EgeSarii/CoroneX/python_code/People-Counting-in-Real-Time-master/Run.py

from mylib.centroidtracker import CentroidTracker
from mylib.trackableobject import TrackableObject
from imutils.video import VideoStream
from imutils.video import FPS
from mylib.mailer import Mailer
from mylib import config, thread
import time, schedule, csv
import numpy as np
import argparse, imutils
import time, dlib, cv2, datetime
from itertools import zip_longest
import Adafruit_DHT
import serial

#co2
import board
import busio
import webbrowser, os, sys


import tkinter as tk

mx=""
my=""
mz=""
ml=""
mu=""

def send():
    global mx,my,mz,ml,mu
    mx=mailField.get()
    my=passField.get()
    mz=sendField.get()
    ml=peopleField.get()
    mu=urlField.get()
    
def startUpWebsites():
    url = "http://192.168.1.156/"

    chrome_path = '/usr/lib/chromium-browser/chromium-browser'
    webbrowser.get(chrome_path).open(url)



#humidity and temperature of the place

t0 = time.time()

def run():
    global mailField,passField, sendField, peopleField, urlField
    mailSender = Mailer()
    
    root = tk.Tk()
    root.configure(bg = '#f4b9b9')
    
    max_amount = 0
    label1 = None #just so it is defined
    label1 = tk.Button(root,text ="START UP HUMIDITY AND TEMPERATURE ENVIRONMENT SETTINGS + AIR QUALITY SENSOR",command = startUpWebsites)
    label1.grid(row=0, column= 1)
    labelMail = tk.Label(root, text="User mail: ")
    labelMail.grid(row=1,column=0)
    labelPass = tk.Label(root, text="User password: ")
    labelPass.grid(row=2,column=0)
    labelSend = tk.Label(root, text="Send to Mail: ")
    labelSend.grid(row=3,column=0)
    labelPeople = tk.Label(root, text="People Limit: ")
    labelPeople.grid(row=4,column=0)
    urlLabel=tk.Label(root, text="IP Cam URL: ")
    urlLabel.grid(row=5,column=0)
    mailField=tk.Entry(root)
    mailField.grid(row=1,column=1,ipadx=100)
    passField=tk.Entry(root)
    passField.grid(row=2,column=1,ipadx=100)
    sendField=tk.Entry(root)
    sendField.grid(row=3,column=1,ipadx=100)
    peopleField=tk.Entry(root)
    peopleField.grid(row=4,column=1,ipadx=100)
    urlField=tk.Entry(root)
    urlField.grid(row=5,column=1,ipadx=100)
    submitValues=tk.Button(text="Submit Values!", command = send)
    submitValues.grid(row=6,column=1, ipadx = 50,padx = 50)
    root.update_idletasks()
    root.update()

    sendToMail = ""
    people_limit = ""
    ipCamUrl = ""

    while(mailSender.EMAIL == "" or mailSender.PASS == "" or sendToMail == "" or people_limit == "" ):
        mailSender.EMAIL=mx
        mailSender.PASS=my
        sendToMail=mz
        people_limit=ml
        ipCamUrl = mu
        root.update()
    
    labelSend.destroy()
    labelMail.destroy()
    labelPass.destroy()
    labelPeople.destroy()
    peopleField.destroy()
    mailField.destroy()
    passField.destroy()
    sendField.destroy()
    submitValues.destroy()
    urlField.destroy()
    urlLabel.destroy()
    label1.destroy()
    
    ct = 0
    counter = tk.Label(root, text = "PEOPLE INSIDE: " + str(ct), width = 1000,bg='White')
    counter.pack(side= 'top' , pady = 80)
    counter.config(font =("Courier",44))

    
    
    enter = tk.Label(root, text = "ENTERING ALLOWED", width = 1000,fg="SpringGreen",bg='White')
    enter.pack(side= 'bottom' , pady = 80)
    enter.config(font =("Courier",60))
  
    
    img = tk.PhotoImage(file="REPRES.png")
    canvas= tk.Label(root, image = img)
    canvas.pack(side ='bottom')
    
    root.attributes('-fullscreen', True)

    # construct the argument parse and parse the arguments
    ap = argparse.ArgumentParser()
    ap.add_argument("-p", "--prototxt", required=False,
        help="path to Caffe 'deploy' prototxt file")
    ap.add_argument("-m", "--model", required=True,
        help="path to Caffe pre-trained model")
    ap.add_argument("-i", "--input", type=str,
        help="path to optional input video file")
    ap.add_argument("-o", "--output", type=str,
        help="path to optional output video file")
    # confidence default 0.4
    ap.add_argument("-c", "--confidence", type=float, default=0.4,
        help="minimum probability to filter weak detections")
    ap.add_argument("-s", "--skip-frames", type=int, default=30,
        help="# of skip frames between detections")
    args = vars(ap.parse_args())

    # initialize the list of class labels MobileNet SSD was trained to
    # detect
    CLASSES = ["background", "aeroplane", "bicycle", "bird", "boat",
        "bottle", "bus", "car", "cat", "chair", "cow", "diningtable",
        "dog", "horse", "motorbike", "person", "pottedplant", "sheep",
        "sofa", "train", "tvmonitor"]

    # load our serialized model from disk
    net = cv2.dnn.readNetFromCaffe(args["prototxt"], args["model"])

    print("[INFO] Starting the video..")
    if(ipCamUrl == ""):
        vs = cv2.VideoCapture(args["input"])
    else:
        vs = cv2.VideoCapture(ipCamUrl)
    # initialize the video writer (we'll instantiate later if need be)
    writer = None

    # initialize the frame dimensions (we'll set them as soon as we read
    # the first frame from the video)
    W = None
    H = None

    # instantiate our centroid tracker, then initialize a list to store
    # each of our dlib correlation trackers, followed by a dictionary to
    # map each unique object ID to a TrackableObject
    ct = CentroidTracker(maxDisappeared=40, maxDistance=50)
    trackers = []
    trackableObjects = {}

    # initialize the total number of frames processed thus far, along
    # with the total number of objects that have moved either up or down
    #NUMBER PEOPLE
    totalFrames = 0
    totalDown = 0
    totalUp = 0
    x = []
    empty=[]
    empty1=[]

    # start the frames per second throughput estimator
    fps = FPS().start()

    if config.Thread:
        vs = thread.ThreadingClass(config.url)

    # loop over frames from the video stream
    ser = serial.Serial('/dev/ttyACM0', 9600)
    while True:
        data = ser.readline().decode('ascii')
        oldSum = sum(x)
        t_end= time.time() + 16
        if(float(data)>=30.5 and float(data)<= 32.5):
                nowImg = tk.PhotoImage(file="download.png")
                canvas.configure(image= nowImg)                                                
                enter.configure(text = "ENTERING IS ALLOWED! :)", width = 1000,fg="SpringGreen")
                # grab the next frame and handle if we are reading from either
                # VideoCapture or VideoStream
                while time.time() < t_end:
                    frame = vs.read()
                    frame = frame[1] if args.get("input", False) else frame

                    # if we are viewing a video and we did not grab a frame then we
                    # have reached the end of the video
                    if args["input"] is not None and frame is None:
                        break

                    # resize the frame to have a maximum width of 500 pixels (the
                    # less data we have, the faster we can process it), then convert
                    # the frame from BGR to RGB for dlib
                    frame = imutils.resize(frame, width = 500)
                    rgb = cv2.cvtColor(frame, cv2.COLOR_BGR2RGB)
    
                    # if the frame dimensions are empty, set them
                    if W is None or H is None:
                        (H, W) = frame.shape[:2]

                    # if we are supposed to be writing a video to disk, initialize
                    # the writer
                    if args["output"] is not None and writer is None:
                        fourcc = cv2.VideoWriter_fourcc(*"MJPG")
                        writer = cv2.VideoWriter(args["output"], fourcc, 30,
                                    (W, H), True)

                    # initialize the current status along with our list of bounding
                    # box rectangles returned by either (1) our object detector or
                    # (2) the correlation trackers
                    status = "Waiting"
                    rects = []

                    # check to see if we should run a more computationally expensive
                    # object detection method to aid our tracker
                    if totalFrames % args["skip_frames"] == 0:
                        # set the status and initialize our new set of object trackers
                        status = "Detecting"
                        trackers = []

                        # convert the frame to a blob and pass the blob through the
                        # network and obtain the detections
                        blob = cv2.dnn.blobFromImage(frame, 0.007843, (W, H), 127.5)
                        net.setInput(blob)
                        detections = net.forward()

                        # loop over the detections
                        for i in np.arange(0, detections.shape[2]):
                                    # extract the confidence (i.e., probability) associated
                                    # with the prediction
                                    confidence = detections[0, 0, i, 2]

                                        # filter out weak detections by requiring a minimum
                                        # confidence
                                    if confidence > args["confidence"]:
                                        # extract the index of the class label from the
                                        # detections list
                                        idx = int(detections[0, 0, i, 1])

                                        # if the class label is not a person, ignore it
                                        if CLASSES[idx] != "person":
                                                    continue

                                        # compute the (x, y)-coordinates of the bounding box
                                        # for the object
                                        box = detections[0, 0, i, 3:7] * np.array([W, H, W, H])
                                        (startX, startY, endX, endY) = box.astype("int")


                                        # construct a dlib rectangle object from the bounding
                                        # box coordinates and then start the dlib correlation
                                        # tracker
                                        tracker = dlib.correlation_tracker()
                                        rect = dlib.rectangle(startX, startY, endX, endY)
                                        tracker.start_track(rgb, rect)

                                        # add the tracker to our list of trackers so we can
                                        # utilize it during skip frames
                                        trackers.append(tracker)

                    # otherwise, we should utilize our object *trackers* rather than
                    # object *detectors* to obtain a higher frame processing throughput
                    else:
                        # loop over the trackers
                        for tracker in trackers:
                                    # set the status of our system to be 'tracking' rather
                                    # than 'waiting' or 'detecting'
                                    status = "Tracking"

                                    # update the tracker and grab the updated position
                                    tracker.update(rgb)
                                    pos = tracker.get_position()

                                    # unpack the position object
                                    startX = int(pos.left())
                                    startY = int(pos.top())
                                    endX = int(pos.right())
                                    endY = int(pos.bottom())

                                    # add the bounding box coordinates to the rectangles lists
                                    rects.append((startX, startY, endX, endY))

                    # draw a horizontal line in the center of the frame -- once an
                    # object crosses this line we will determine whether they were
                    # moving 'up' or 'down'
                    cv2.line(frame, (0, H // 2), (W, H // 2), (0, 0, 0), 3)
                    cv2.putText(frame, "-Prediction border - Entrance-", (10, H - ((i * 20) + 200)),
                        cv2.FONT_HERSHEY_SIMPLEX, 0.5, (0, 0, 0), 1)

                    # use the centroid tracker to associate the (1) old object
                    # centroids with (2) the newly computed object centroids
                    objects = ct.update(rects)

                    # loop over the tracked objects
                    for (objectID, centroid) in objects.items():
                        # check to see if a trackable object exists for the current
                        # object ID
                        to = trackableObjects.get(objectID, None)

                        # if there is no existing trackable object, create one
                        if to is None:
                                    to = TrackableObject(objectID, centroid)

                        # otherwise, there is a trackable object so we can utilize it
                        # to determine direction
                        else:
                                    # the difference between the y-coordinate of the *current*
                                    # centroid and the mean of *previous* centroids will tell
                                    # us in which direction the object is moving (negative for
                                    # 'up' and positive for 'down')
                                    y = [c[1] for c in to.centroids]
                                    direction = centroid[1] - np.mean(y)
                                    to.centroids.append(centroid)

                                    # check to see if the object has been counted or not
                                    if not to.counted:
                                        # if the direction is negative (indicating the object
                                        # is moving up) AND the centroid is above the center
                                        # line, count the object
                                        if direction < 0 and centroid[1] < H // 2:
                                                    totalUp += 1
                                                    empty.append(totalUp)
                                                    to.counted = True

                                        # if the direction is positive (indicating the object
                                        # is moving down) AND the centroid is below the
                                        # center line, count the object
                                        elif direction > 0 and centroid[1] > H // 2:
                                                    totalDown += 1
                                                    empty1.append(totalDown)
                                                    #print(empty1[-1])
                                                    x = []
                                                    # compute the sum of total people inside
                                                    x.append(len(empty1)-len(empty))
                                                    #print("Total people inside:", x)
                                                    # Optimise number below: 10, 50, 100, etc., indicate the max. people inside limit
                                                    # if the limit exceeds, send an email alert
                                                    
                                                    if sum(x) == int(people_limit):
                                                        if config.ALERT:
                                                                    print("[INFO] Sending email alert..")
                                                                    mailSender.send(sendToMail)
                                                                    print("[INFO] Alert sent")

                                                    to.counted = True
                                                    
                                        
                                        if(sum(x) < int(people_limit)):
                                                    nowImg = tk.PhotoImage(file="download.png")
                                                    canvas.configure(image= nowImg)                                                
                                                    enter.configure(text = "ENTERING IS ALLOWED! :)", width = 1000,fg="SpringGreen")
                                        else:
                                                    nowImg = tk.PhotoImage(file="REPRES.png")
                                                    canvas.configure(image= nowImg)  
                                                    enter.configure(text = "FULL INSIDE, YOU CAN'T ENTER!!!", width = 1000, fg="red")
                                                    
                                                    
                                        counter.configure(text= "PEOPLE INSIDE: " + str(sum(x)),width = 1000)
                                        

                        # store the trackable object in our dictionary
                        trackableObjects[objectID] = to

                        # draw both the ID of the object and the centroid of the
                        # object on the output frame
                        text = "ID {}".format(objectID)
                        cv2.putText(frame, text, (centroid[0] - 10, centroid[1] - 10),
                                    cv2.FONT_HERSHEY_SIMPLEX, 0.5, (255, 255, 255), 2)
                        cv2.circle(frame, (centroid[0], centroid[1]), 4, (255, 255, 255), -1)

                    # construct a tuple of information we will be displaying on the
                    info = [
                    ("Exit", totalUp),
                    ("Enter", totalDown),
                    ("Status", status),
                    ]

                    info2 = [
                    ("Total people inside",  x),
                    ]
                    
                                    # Display the output
                    for (i, (k, v)) in enumerate(info):
                        text = "{}: {}".format(k, v)
                        cv2.putText(frame, text, (10, H - ((i * 20) + 20)), cv2.FONT_HERSHEY_SIMPLEX, 0.6, (0, 0, 0), 2)

                    for (i, (k, v)) in enumerate(info2):
                        text = "{}: {}".format(k, v)
                        cv2.putText(frame, text, (265, H - ((i * 20) + 60)), cv2.FONT_HERSHEY_SIMPLEX, 0.6, (255, 255, 255), 2)

                    # Initiate a simple log to save data at end of the day
                    if config.Log:
                        datetimee = [datetime.datetime.now()]
                        d = [datetimee, empty1, empty, x]
                        export_data = zip_longest(*d, fillvalue = '')

                        with open('Log.csv', 'w', newline='') as myfile:
                                    wr = csv.writer(myfile, quoting=csv.QUOTE_ALL)
                                    wr.writerow(("End Time", "In", "Out", "Total Inside"))
                                    wr.writerows(export_data)


                    # show the output frame
                    cv2.imshow("Real-Time Monitoring/Analysis Window", frame)
                    key = cv2.waitKey(1) & 0xFF

                    # if the `q` key was pressed, break from the loop
                    if key == ord('q'):
                        break

                    # increment the total number of frames processed thus far and
                    # then update the FPS counter
                    totalFrames += 1
                    fps.update()
            
                    if config.Timer:
                        # Automatic timer to stop the live stream. Set to 8 hours (28800s).
                        t1 = time.time()
                        num_seconds=(t1-t0)
                        if num_seconds > 28800:
                                    break
                                
                    if sum(x) >= oldSum+1:
                        nowImg = tk.PhotoImage(file="REPRES.png")
                        canvas.configure(image= nowImg)   
                        break
                    
                    root.update()
                    
        elif(float(data)>37.8):
            mailSender.sendHighTemperature(sendToMail)
            #send temperature warning mail
        else:
                nowImg = tk.PhotoImage(file="REPRES.png")
                canvas.configure(image= nowImg) 
                # grab the next frame and handle if we are reading from either
                # VideoCapture or VideoStream
                frame = vs.read()
                frame = frame[1] if args.get("input", False) else frame

                # if we are viewing a video and we did not grab a frame then we
                # have reached the end of the video
                if args["input"] is not None and frame is None:
                    break

                # resize the frame to have a maximum width of 500 pixels (the
                # less data we have, the faster we can process it), then convert
                # the frame from BGR to RGB for dlib
                frame = imutils.resize(frame, width = 500)
                rgb = cv2.cvtColor(frame, cv2.COLOR_BGR2RGB)

                # if the frame dimensions are empty, set them
                if W is None or H is None:
                    (H, W) = frame.shape[:2]

                # if we are supposed to be writing a video to disk, initialize
                # the writer
                if args["output"] is not None and writer is None:
                    fourcc = cv2.VideoWriter_fourcc(*"MJPG")
                    writer = cv2.VideoWriter(args["output"], fourcc, 30,
                                (W, H), True)

                # initialize the current status along with our list of bounding
                # box rectangles returned by either (1) our object detector or
                # (2) the correlation trackers
                status = "Waiting"
                rects = []

                # check to see if we should run a more computationally expensive
                # object detection method to aid our tracker
                if totalFrames % args["skip_frames"] == 0:
                    # set the status and initialize our new set of object trackers
                    status = "Detecting"
                    trackers = []

                    # convert the frame to a blob and pass the blob through the
                    # network and obtain the detections
                    blob = cv2.dnn.blobFromImage(frame, 0.007843, (W, H), 127.5)
                    net.setInput(blob)
                    detections = net.forward()

                    # loop over the detections
                    for i in np.arange(0, detections.shape[2]):
                                # extract the confidence (i.e., probability) associated
                                # with the prediction
                                confidence = detections[0, 0, i, 2]

                                # filter out weak detections by requiring a minimum
                                # confidence
                                if confidence > args["confidence"]:
                                    # extract the index of the class label from the
                                    # detections list
                                    idx = int(detections[0, 0, i, 1])

                                    # if the class label is not a person, ignore it
                                    if CLASSES[idx] != "person":
                                                continue

                                    # compute the (x, y)-coordinates of the bounding box
                                    # for the object
                                    box = detections[0, 0, i, 3:7] * np.array([W, H, W, H])
                                    (startX, startY, endX, endY) = box.astype("int")


                                    # construct a dlib rectangle object from the bounding
                                    # box coordinates and then start the dlib correlation
                                    # tracker
                                    tracker = dlib.correlation_tracker()
                                    rect = dlib.rectangle(startX, startY, endX, endY)
                                    tracker.start_track(rgb, rect)

                                    # add the tracker to our list of trackers so we can
                                    # utilize it during skip frames
                                    trackers.append(tracker)

                # otherwise, we should utilize our object *trackers* rather than
                # object *detectors* to obtain a higher frame processing throughput
                else:
                    # loop over the trackers
                    for tracker in trackers:
                                # set the status of our system to be 'tracking' rather
                                # than 'waiting' or 'detecting'
                                status = "Tracking"

                                # update the tracker and grab the updated position
                                tracker.update(rgb)
                                pos = tracker.get_position()

                                # unpack the position object
                                startX = int(pos.left())
                                startY = int(pos.top())
                                endX = int(pos.right())
                                endY = int(pos.bottom())

                                # add the bounding box coordinates to the rectangles lists
                                rects.append((startX, startY, endX, endY))

                # draw a horizontal line in the center of the frame -- once an
                # object crosses this line we will determine whether they were
                # moving 'up' or 'down'
                cv2.line(frame, (0, H // 2), (W, H // 2), (0, 0, 0), 3)
                cv2.putText(frame, "-Prediction border - Entrance-", (10, H - ((i * 20) + 200)),
                    cv2.FONT_HERSHEY_SIMPLEX, 0.5, (0, 0, 0), 1)

                # use the centroid tracker to associate the (1) old object
                # centroids with (2) the newly computed object centroids
                objects = ct.update(rects)

                # loop over the tracked objects
                for (objectID, centroid) in objects.items():
                    # check to see if a trackable object exists for the current
                    # object ID
                    to = trackableObjects.get(objectID, None)

                    # if there is no existing trackable object, create one
                    if to is None:
                                to = TrackableObject(objectID, centroid)

                    # otherwise, there is a trackable object so we can utilize it
                    # to determine direction
                    else:
                                # the difference between the y-coordinate of the *current*
                                # centroid and the mean of *previous* centroids will tell
                                # us in which direction the object is moving (negative for
                                # 'up' and positive for 'down')
                                y = [c[1] for c in to.centroids]
                                direction = centroid[1] - np.mean(y)
                                to.centroids.append(centroid)

                                # check to see if the object has been counted or not
                                if not to.counted:
                                    # if the direction is negative (indicating the object
                                    # is moving up) AND the centroid is above the center
                                    # line, count the object
                                    if direction < 0 and centroid[1] < H // 2:
                                                totalUp += 1
                                                empty.append(totalUp)
                                                to.counted = True

                                    # if the direction is positive (indicating the object
                                    # is moving down) AND the centroid is below the
                                    # center line, count the object
                                    elif direction > 0 and centroid[1] > H // 2:
                                                totalDown += 1
                                                empty1.append(totalDown)
                                                #print(empty1[-1])
                                                x = []
                                                # compute the sum of total people inside
                                                x.append(len(empty1)-len(empty))
                                                #print("Total people inside:", x)
                                                # Optimise number below: 10, 50, 100, etc., indicate the max. people inside limit
                                                # if the limit exceeds, send an email alert
                                                
                                                if sum(x) == int(people_limit):
                                                    if config.ALERT:
                                                                print("[INFO] Sending email alert..")
                                                                mailSender.send(sendToMail)
                                                                print("[INFO] Alert sent")

                                                to.counted = True
                                                
                                    
                                    
                                    if(sum(x)<int(people_limit)):                                             
                                                enter.configure(text = "ENTERING IS ALLOWED! :)", width = 1000,fg="SpringGreen")
                                    else:
                                                 
                                                enter.configure(text = "FULL INSIDE, YOU CAN'T ENTER!!!", width = 1000, fg="red")
                                                
                                                
                                    counter.configure(text= "PEOPLE INSIDE: " + str(sum(x)),width = 1000)


                    # store the trackable object in our dictionary
                    trackableObjects[objectID] = to

                    # draw both the ID of the object and the centroid of the
                    # object on the output frame
                    text = "ID {}".format(objectID)
                    cv2.putText(frame, text, (centroid[0] - 10, centroid[1] - 10),
                                cv2.FONT_HERSHEY_SIMPLEX, 0.5, (255, 255, 255), 2)
                    cv2.circle(frame, (centroid[0], centroid[1]), 4, (255, 255, 255), -1)

                # construct a tuple of information we will be displaying on the
                info = [
                ("Exit", totalUp),
                ("Enter", totalDown),
                ("Status", status),
                ]

                info2 = [
                ("Total people inside", x),
                ]
                
                                # Display the output
                for (i, (k, v)) in enumerate(info):
                    text = "{}: {}".format(k, v)
                    cv2.putText(frame, text, (10, H - ((i * 20) + 20)), cv2.FONT_HERSHEY_SIMPLEX, 0.6, (0, 0, 0), 2)

                for (i, (k, v)) in enumerate(info2):
                    text = "{}: {}".format(k, v)
                    cv2.putText(frame, text, (265, H - ((i * 20) + 60)), cv2.FONT_HERSHEY_SIMPLEX, 0.6, (255, 255, 255), 2)

                # Initiate a simple log to save data at end of the day
                if config.Log:
                    datetimee = [datetime.datetime.now()]
                    d = [datetimee, empty1, empty, x]
                    export_data = zip_longest(*d, fillvalue = '')

                    with open('Log.csv', 'w', newline='') as myfile:
                                wr = csv.writer(myfile, quoting=csv.QUOTE_ALL)
                                wr.writerow(("End Time", "In", "Out", "Total Inside"))
                                wr.writerows(export_data)


                # show the output frame
                cv2.imshow("Real-Time Monitoring/Analysis Window", frame)
                key = cv2.waitKey(1) & 0xFF

                # if the `q` key was pressed, break from the loop
                if key == ord('q'):
                    break

                # increment the total number of frames processed thus far and
                # then update the FPS counter
                totalFrames += 1
                fps.update()

                if config.Timer:
                    # Automatic timer to stop the live stream. Set to 8 hours (28800s).
                    t1 = time.time()
                    num_seconds=(t1-t0)
                    if num_seconds > 28800:
                                break
                            
                if sum(x) >= oldSum+1: #illegal entering
                        mailSender.sendIllegalIncrement(sendToMail)
                
                root.update()
            

    # stop the timer and display FPS information
    fps.stop()
    print("[INFO] elapsed time: {:.2f}".format(fps.elapsed()))
    print("[INFO] approx. FPS: {:.2f}".format(fps.fps()))


    # # if we are not using a video file, stop the camera video stream
    # if not args.get("input", False):
    #   vs.stop()
    #
    # # otherwise, release the video file pointer
    # else:
    #   vs.release()

    # close any open windows
    cv2.destroyAllWindows()


##learn more about different schedules here: https://pypi.org/project/schedule/
if config.Scheduler:
    ##Runs for every 1 second
    #schedule.every(1).seconds.do(run)
    ##Runs at every day (9:00 am). You can change it.
    schedule.every().day.at("9:00").do(run)

    while 1:
        schedule.run_pending()

else:
    run()
